Chobrenga/N64-SpyDVI/Images/V2_2/Board3DNC.png

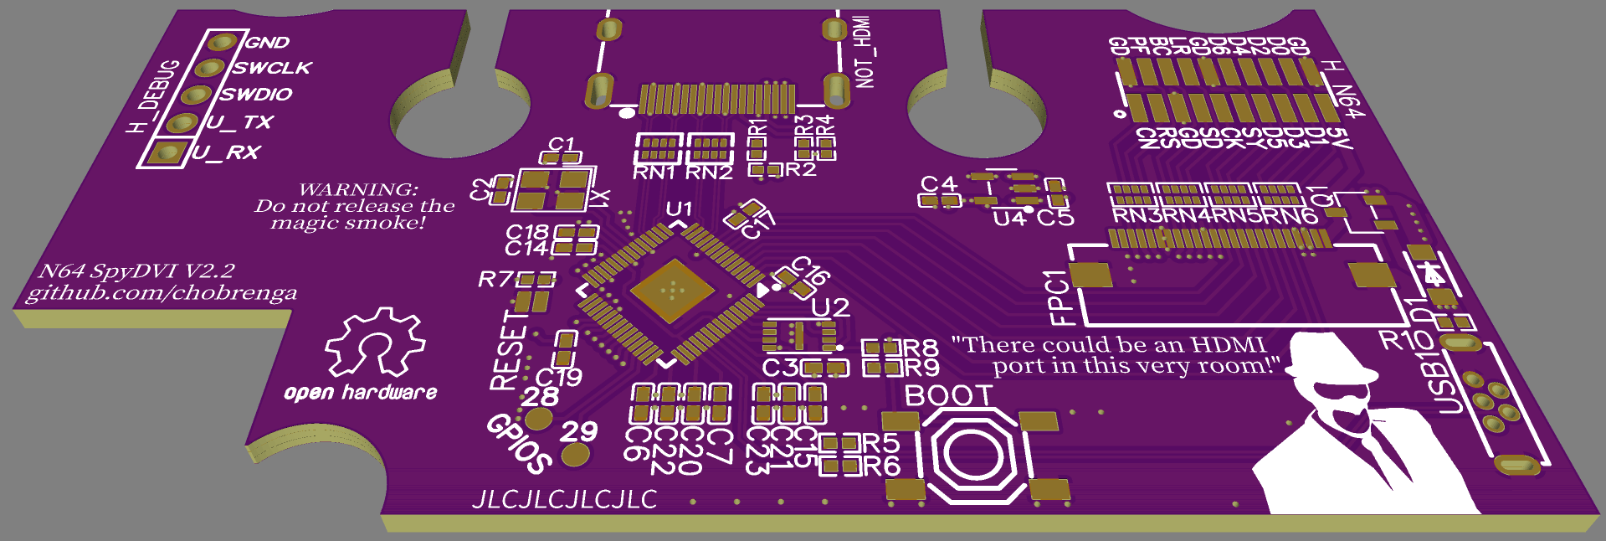
Images/V2_2/Board3DNC.png
