Chobrenga/N64-SpyDVI/Images/V2_2/BRDBack.png

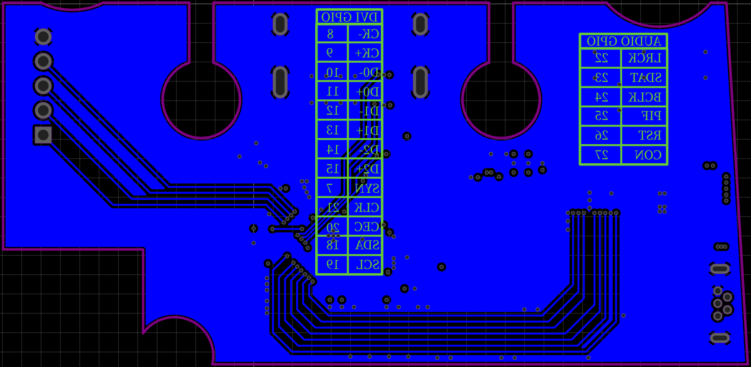
Images/V2_2/BRDBack.png
