Chobrenga/N64-SpyDVI/Images/V2_2/BRDFront.png

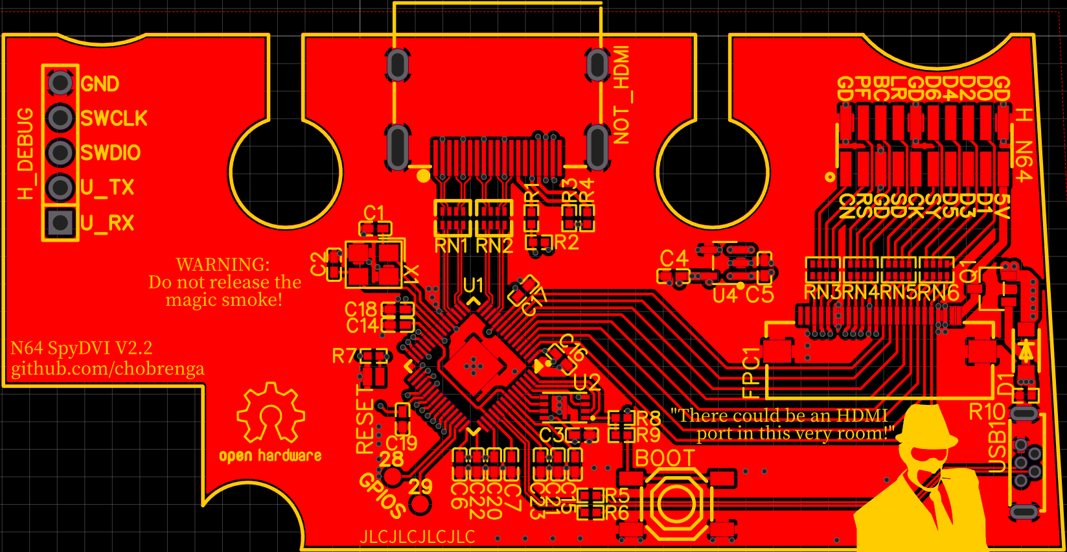
Images/V2_2/BRDFront.png
