Chobrenga/N64-SpyDVI/Software/libdvi/audio_ring.h

#ifndef AUDIO_RING_H
#define AUDIO_RING_H
#include "pico.h"

typedef struct audio_sample {
    int16_t channels[2];
} audio_sample_t;

typedef struct audio_sample_u {
    uint16_t channels[2];
} audio_sample_u_t;

typedef struct audio_ring {
    audio_sample_t    *buffer;
    uint32_t          size;
    volatile uint32_t read;
    volatile uint32_t write; 
} audio_ring_t;

inline audio_sample_t *get_buffer_top(audio_ring_t *audio_ring)    { return audio_ring->buffer; }
inline uint32_t get_buffer_size(audio_ring_t *audio_ring)          { return audio_ring->size;   }
inline uint32_t get_read_offset(audio_ring_t *audio_ring)          { return audio_ring->read;   }
inline uint32_t get_write_offset(audio_ring_t *audio_ring)         { return audio_ring->write;  }
inline audio_sample_t *get_write_pointer(audio_ring_t *audio_ring) { return audio_ring->buffer + audio_ring->write; }
inline audio_sample_t *get_read_pointer(audio_ring_t *audio_ring)  { return audio_ring->buffer + audio_ring->read;  }
void increase_write_pointer(audio_ring_t *audio_ring, uint32_t size);
void increase_read_pointer(audio_ring_t *audio_ring, uint32_t size);
void audio_ring_set(audio_ring_t *audio_ring, audio_sample_t *buffer, uint32_t size);
uint32_t get_write_size(audio_ring_t *audio_ring, bool full);
uint32_t get_read_size(audio_ring_t *audio_ring, bool full);
void set_write_offset(audio_ring_t *audio_ring, uint32_t v);
void set_read_offset(audio_ring_t *audio_ring, uint32_t v);
#endif
